xxpESP32/T12/程序源码/HARDWARE/OLED/bmp.h

#ifndef __BMP_H
#define __BMP_H
unsigned char BMP1[] =

{0x00,0x00,0x00,0x00,0x00,0x00,0x00,0x00,0xF8,0xF8,0x00,0x00,0x00,0x00,0xF8,0xF8,0x70,0xE0,0xC0,0x80,0x00,0x00,0x00,0x00,0x00,0x00,0x00,0xC0,0xC0,0x80,0x00,0x00,0xFF,0xFF,0x00,0x00,0x00,0x00,0xFF,0xFF,0x00,0x00,0x01,0x03,0x03,0x00,0x00,0x00,0x00,0x00,0x00,0x00,0x01,0x03,0x07,0x0E,0x1F,0x1F,0x00,0x00,0x00,0x00,0x1F,0x1F,0x00,0x00,0x00,0x00,0x00,0x00,0x00,0x00};/*"C:\Users\xwp\Desktop\电烙铁\传输列表.bmp",0*/



#endif
